ethan-se/ucl-east-food-queue-gauge/digitalTwin/Assets/images/Marshagte canteen.jpg

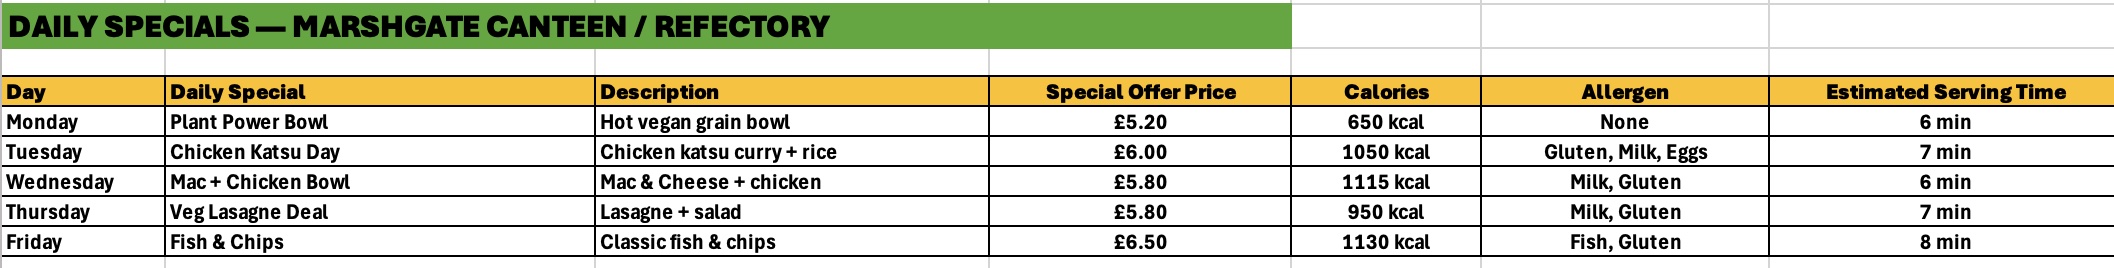
digitalTwin/Assets/images/Marshagte canteen.jpg
