ethan-se/ucl-east-food-queue-gauge/digitalTwin/Assets/images/Marshgate cafe.png

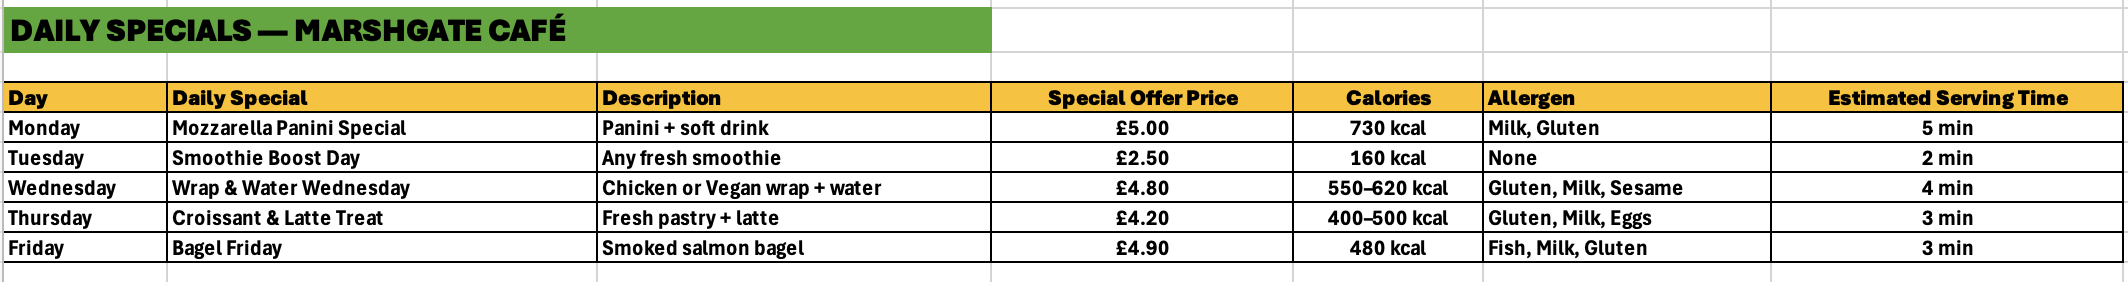
digitalTwin/Assets/images/Marshgate cafe.png
