ethan-se/ucl-east-food-queue-gauge/digitalTwin/Assets/images/Pool st .png

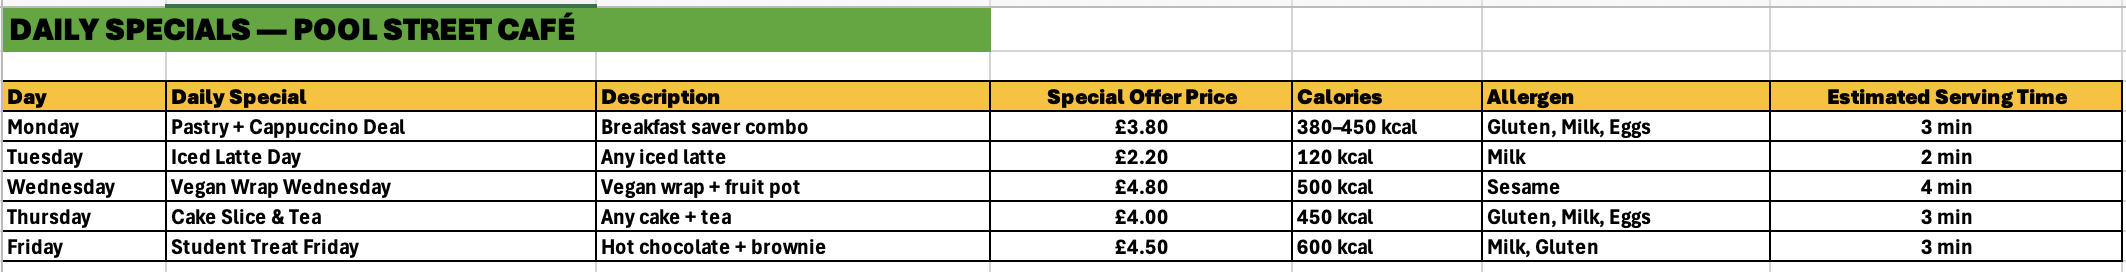
digitalTwin/Assets/images/Pool st .png
