ethan-se/ucl-east-food-queue-gauge/digitalTwin/Assets/Screenshot 2025-12-09 at 11.29.18.png

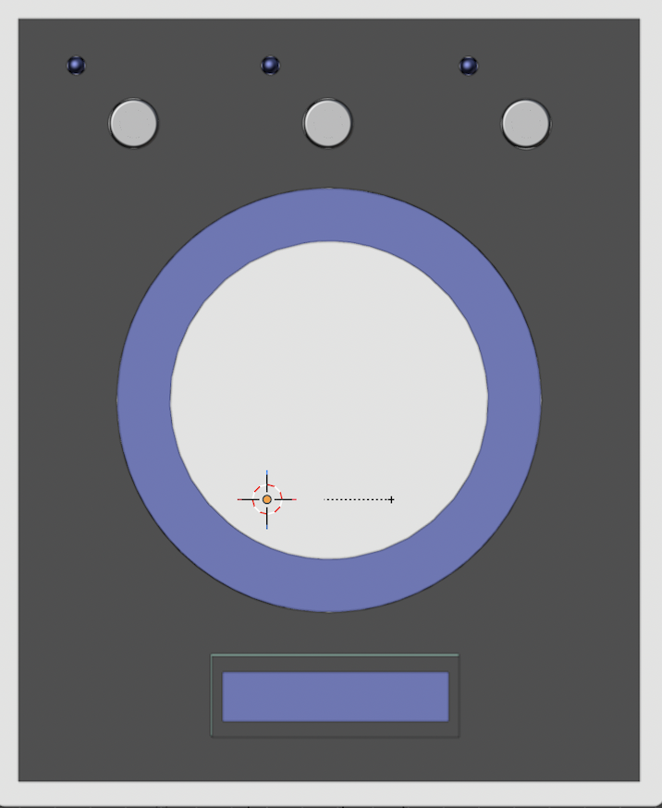
digitalTwin/Assets/Screenshot 2025-12-09 at 11.29.18.png
