ethan-se/ucl-east-food-queue-gauge/docs/render-0.png

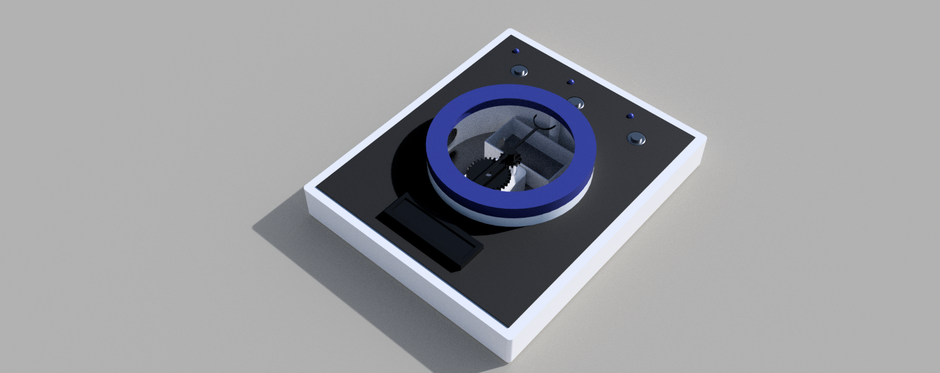
docs/render-0.png
